svenpetersen1965/VIC-20-Hyper-Expander/Rev. 0/pictures/6766_Hyper_Expander_in_tfw8bit_case.JPG

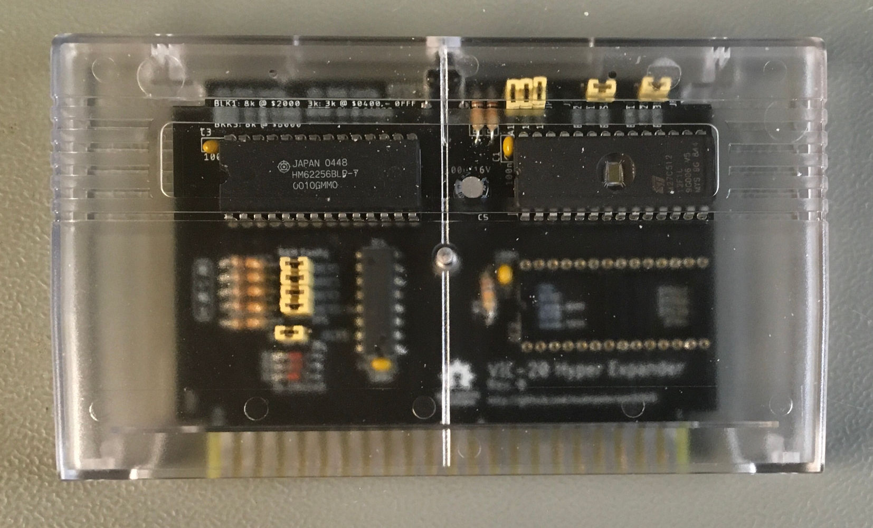
Rev. 0/pictures/6766_Hyper_Expander_in_tfw8bit_case.JPG
