svenpetersen1965/VIC-20-Hyper-Expander/Rev. 1/pictures/8315_-_DOOM.JPG

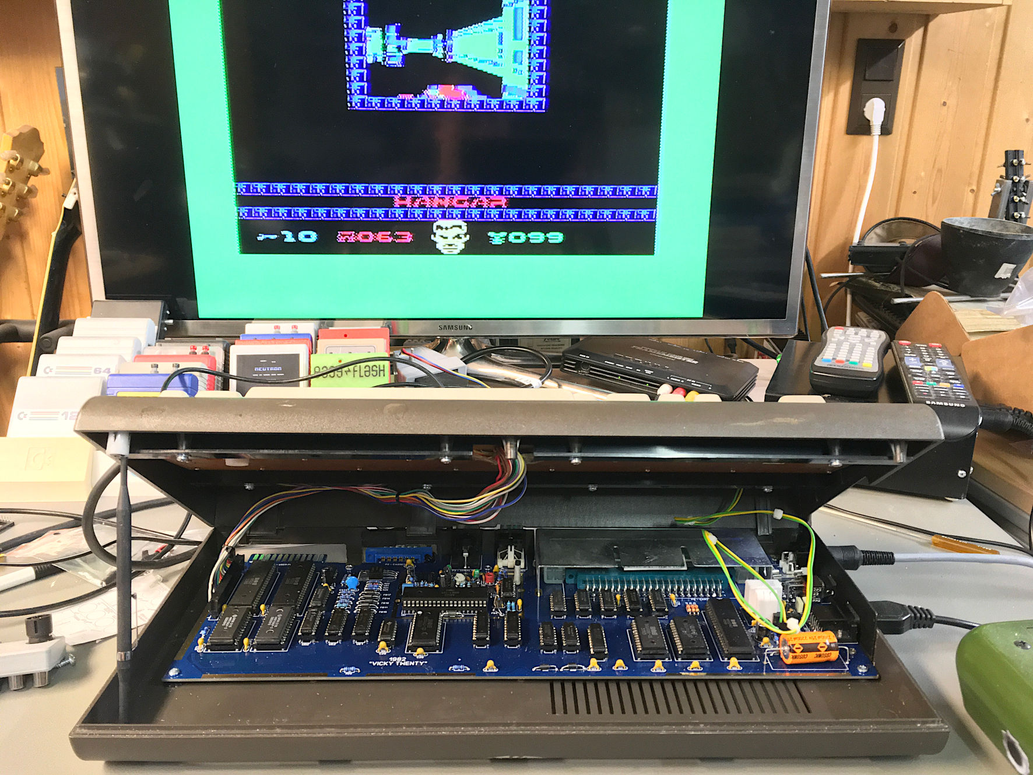
Rev. 1/pictures/8315_-_DOOM.JPG
