svenpetersen1965/VIC-20-Hyper-Expander/Rev. 2/pictures/9388_-_Hyper_Expander_v2_RAMonly.JPG

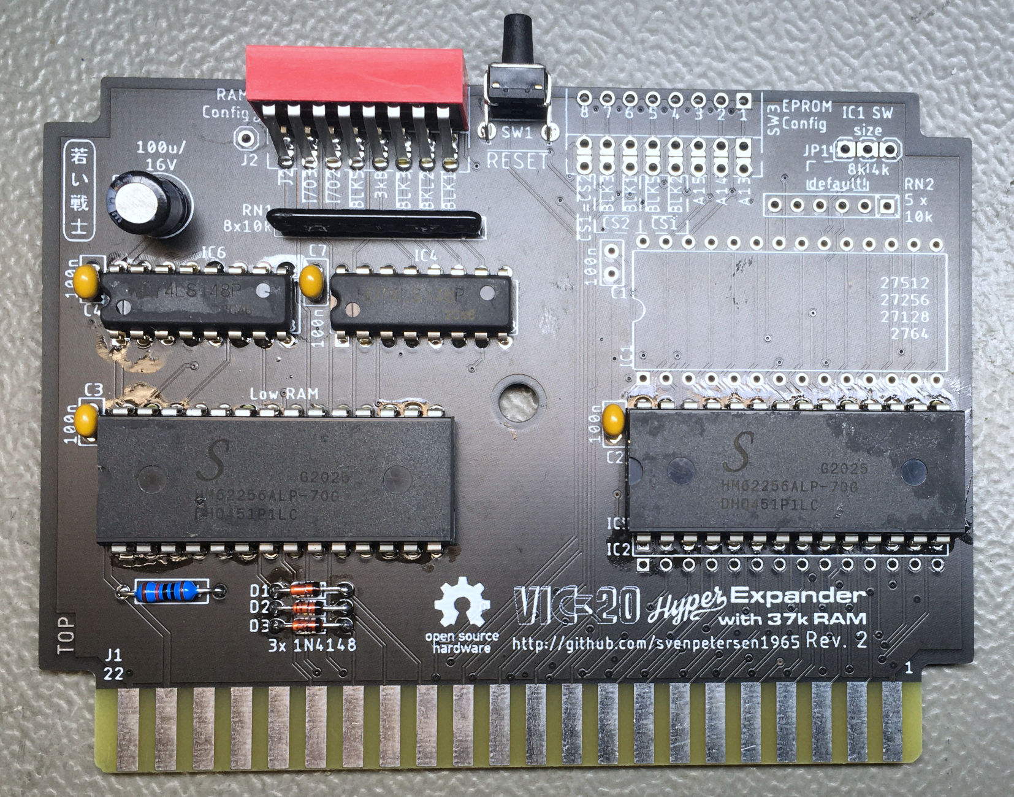
Rev. 2/pictures/9388_-_Hyper_Expander_v2_RAMonly.JPG
