svenpetersen1965/VIC-20-Hyper-Expander/Rev. 2/pictures/9523_-_case_cutout.JPG

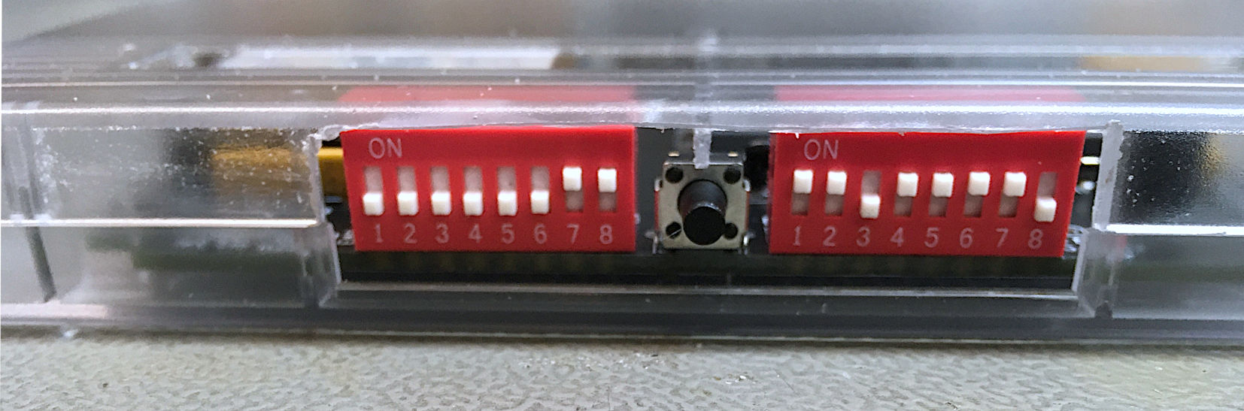
Rev. 2/pictures/9523_-_case_cutout.JPG
