svenpetersen1965/VIC-20-Hyper-Expander/Rev. 2/pictures/9525_-_case_connector.JPG

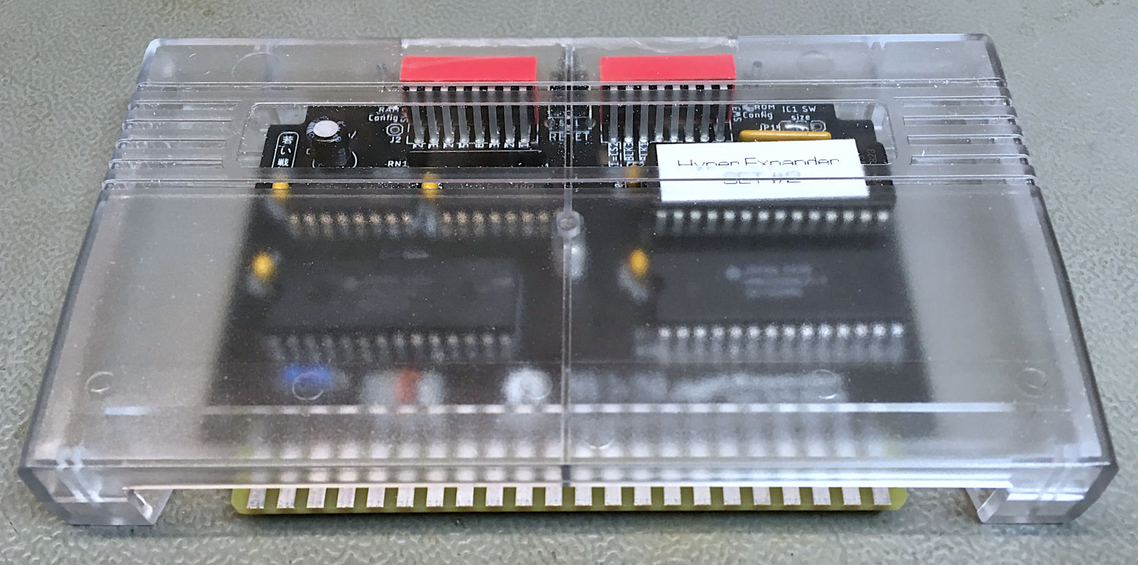
Rev. 2/pictures/9525_-_case_connector.JPG
