svenpetersen1965/VIC-20-Hyper-Expander/Rev. 2/pictures/9766_-_single_in_case.JPG

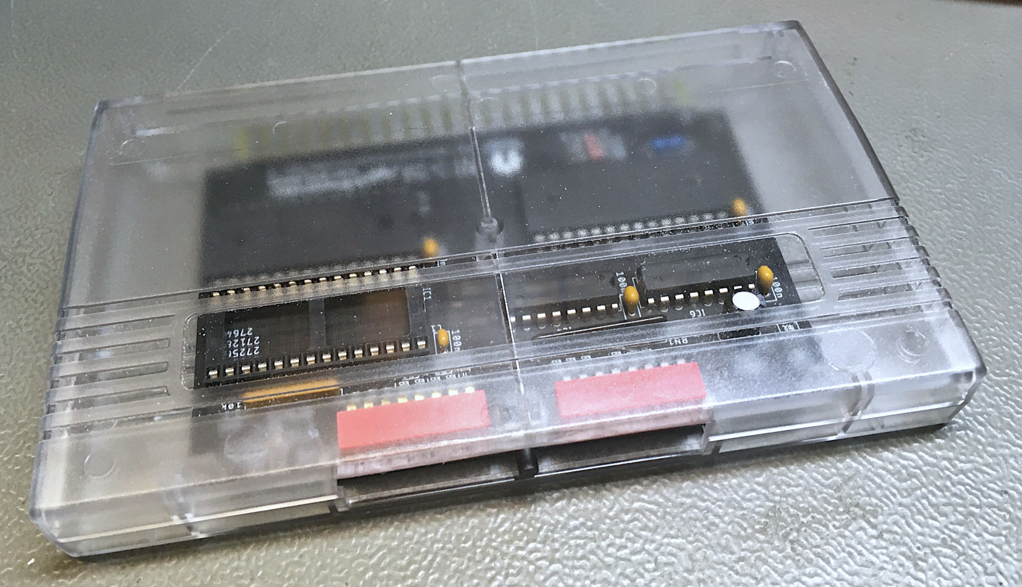
Rev. 2/pictures/9766_-_single_in_case.JPG
