svenpetersen1965/VIC-20-Hyper-Expander/Rev. 2/pictures/BASIC_FORTH_VICTERM.jpg

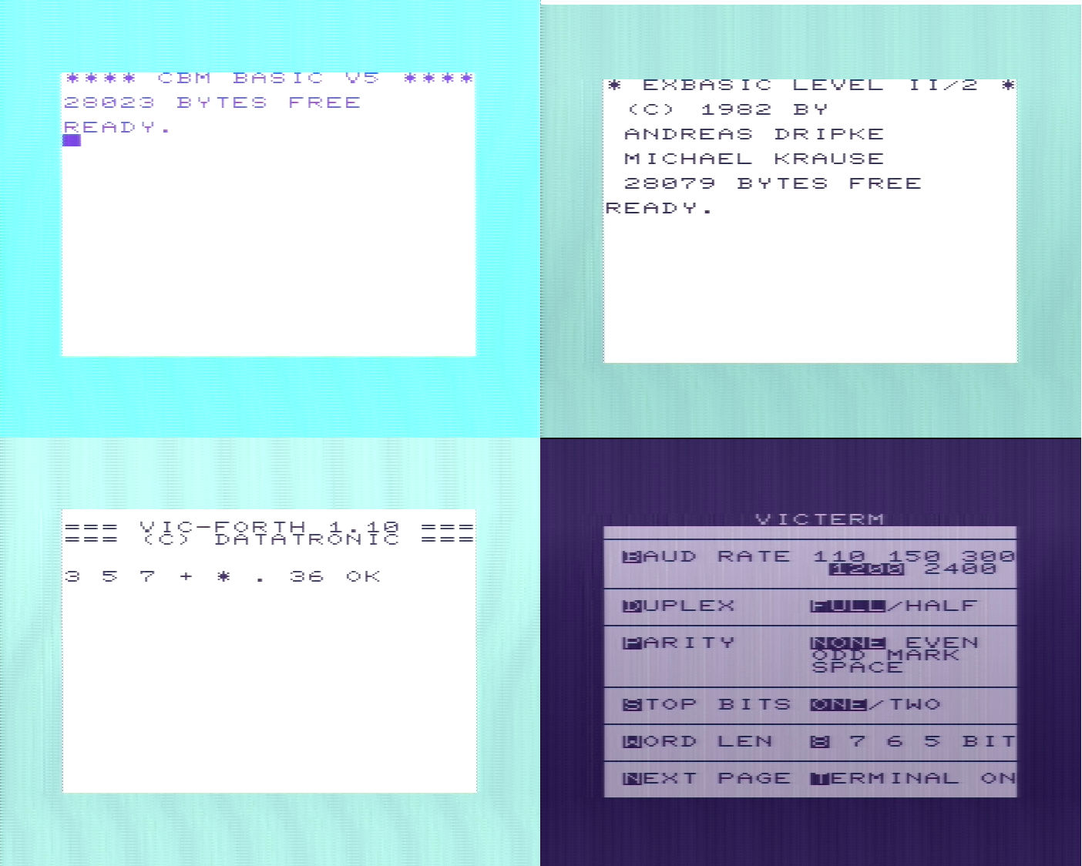
Rev. 2/pictures/BASIC_FORTH_VICTERM.jpg
