svenpetersen1965/VIC-20-Hyper-Expander/Rev. 2/pictures/BASIC_V5.png

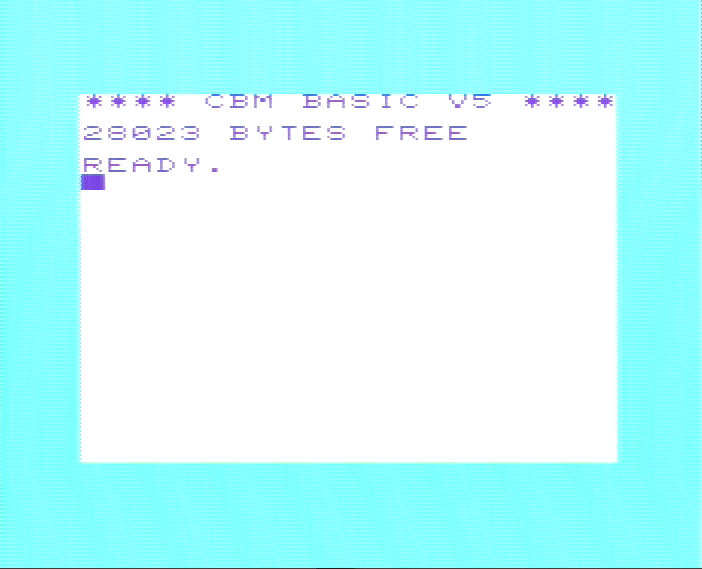
Rev. 2/pictures/BASIC_V5.png
