svenpetersen1965/VIC-20-Hyper-Expander/Rev. 2/pictures/buck_def_load_mspac.jpg

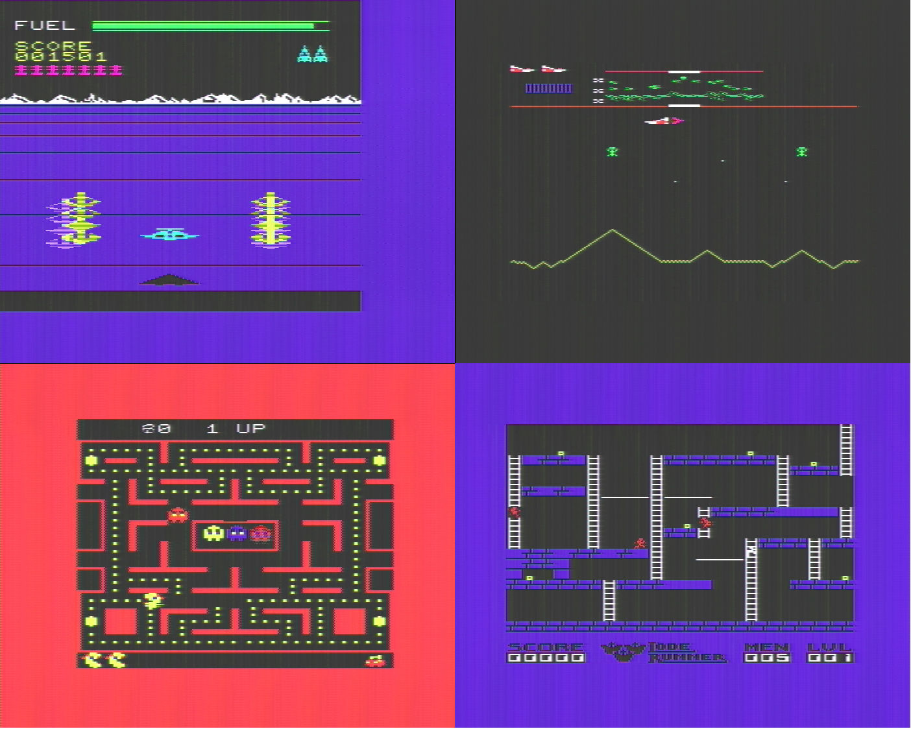
Rev. 2/pictures/buck_def_load_mspac.jpg
