svenpetersen1965/VIC-20-Hyper-Expander/Rev. 2/pictures/buckrogers.png

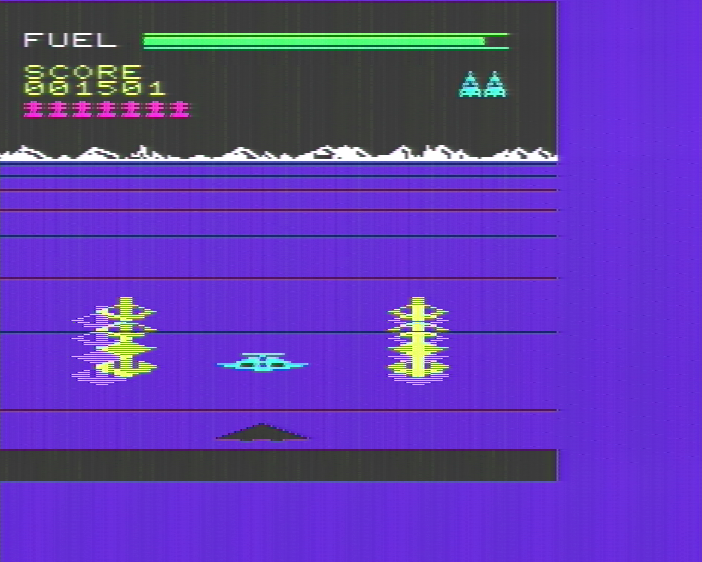
Rev. 2/pictures/buckrogers.png
