svenpetersen1965/VIC-20-Hyper-Expander/Rev. 2/pictures/ExBASIC_L2.png

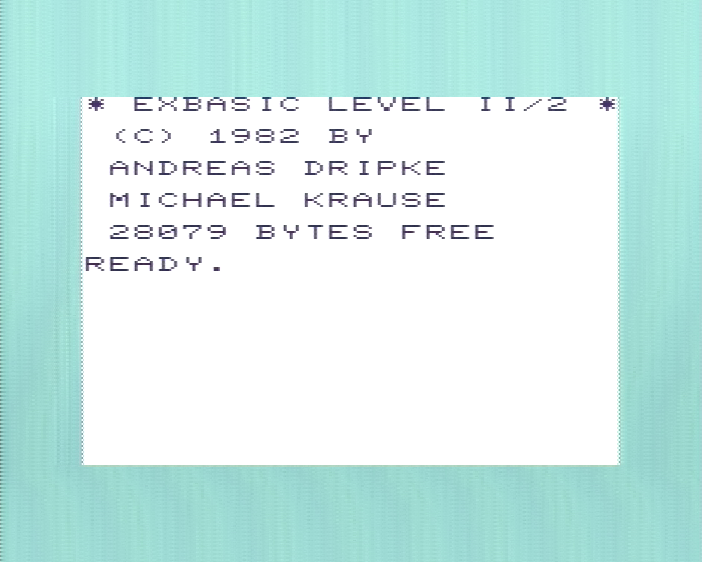
Rev. 2/pictures/ExBASIC_L2.png
