svenpetersen1965/VIC-20-Hyper-Expander/Rev. 2/pictures/mspacman.png

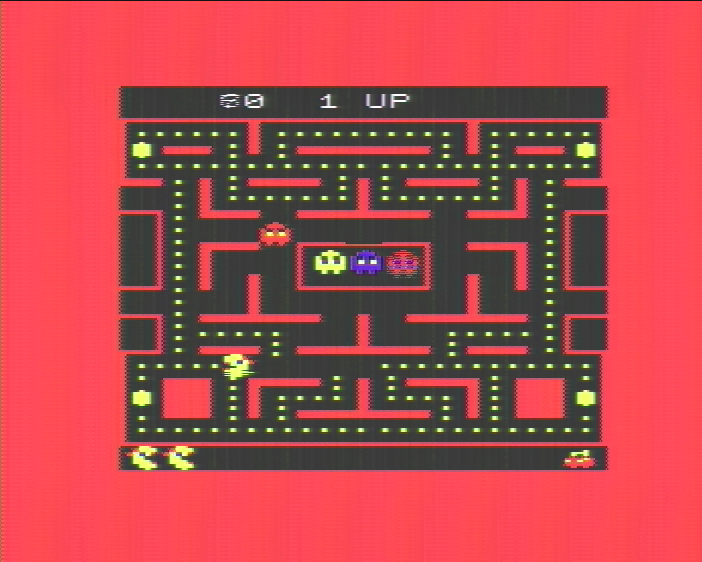
Rev. 2/pictures/mspacman.png
