svenpetersen1965/VIC-20-Hyper-Expander/Rev. 2/pictures/SExp_Diag.jpg

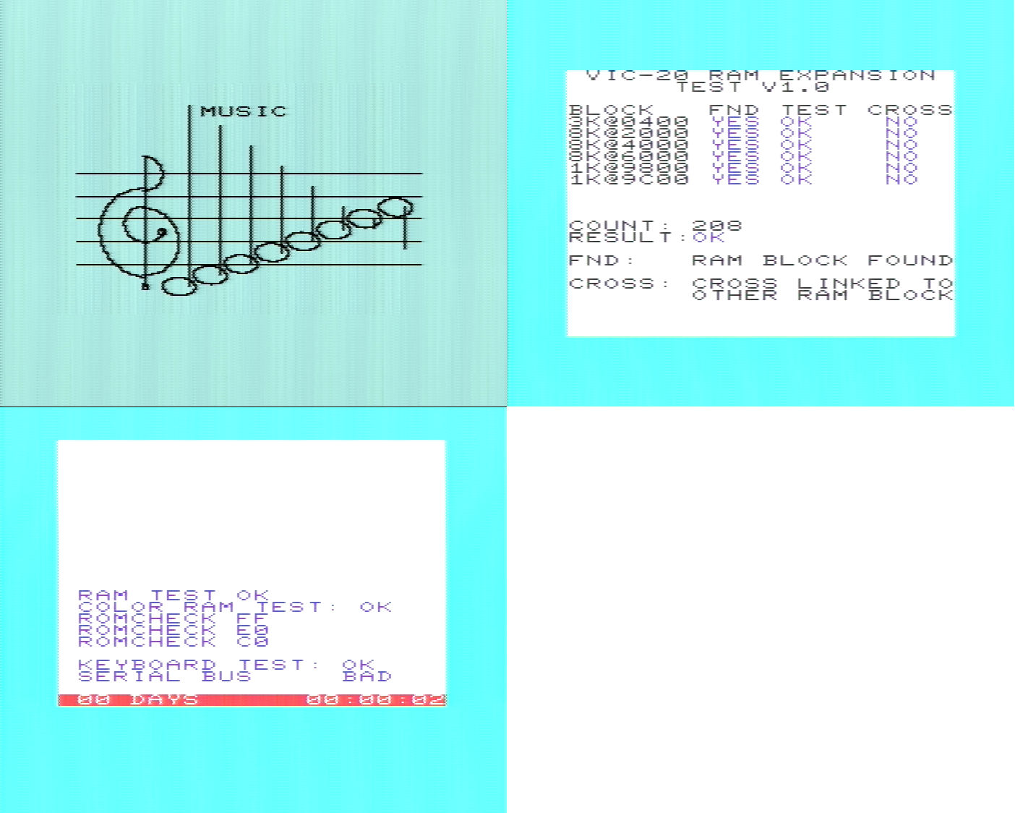
Rev. 2/pictures/SExp_Diag.jpg
