svenpetersen1965/VIC-20-Hyper-Expander/Rev. 2/pictures/vic20diag.png

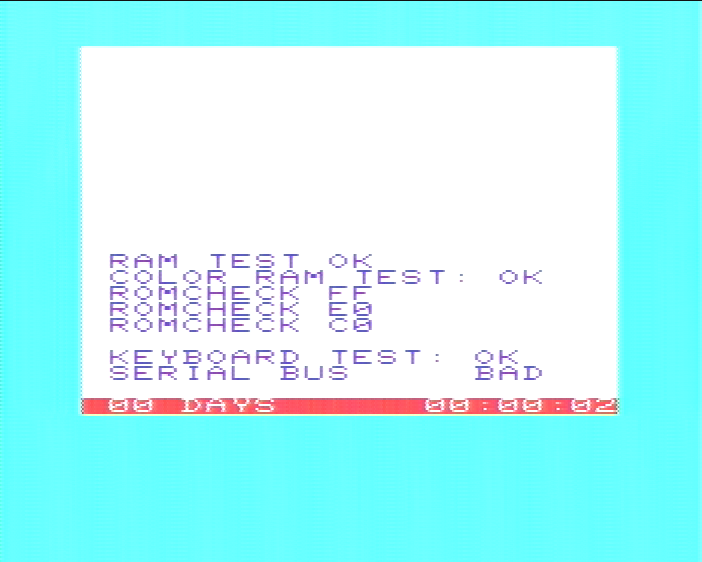
Rev. 2/pictures/vic20diag.png
