svenpetersen1965/VIC-20-Hyper-Expander/Rev. 2/pictures/VIC-FORTH.png

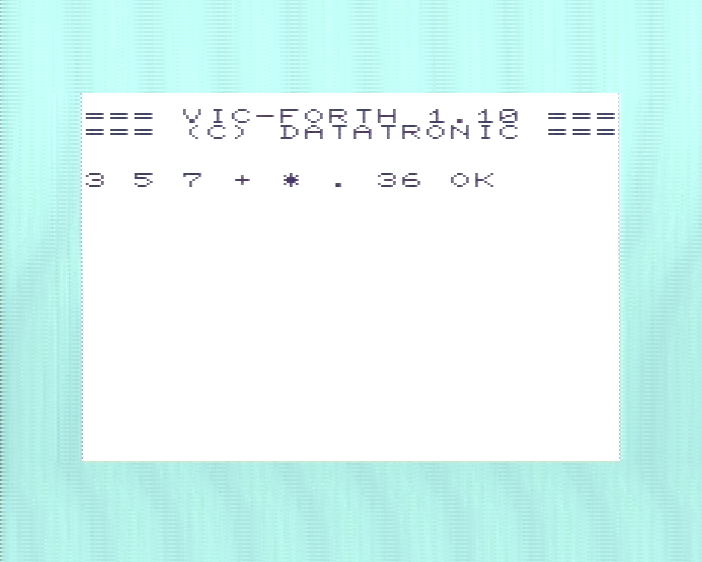
Rev. 2/pictures/VIC-FORTH.png
