svenpetersen1965/VIC-20-Hyper-Expander/Rev. 1/pictures/8356_-_Super_Expander_Software_Test.JPG

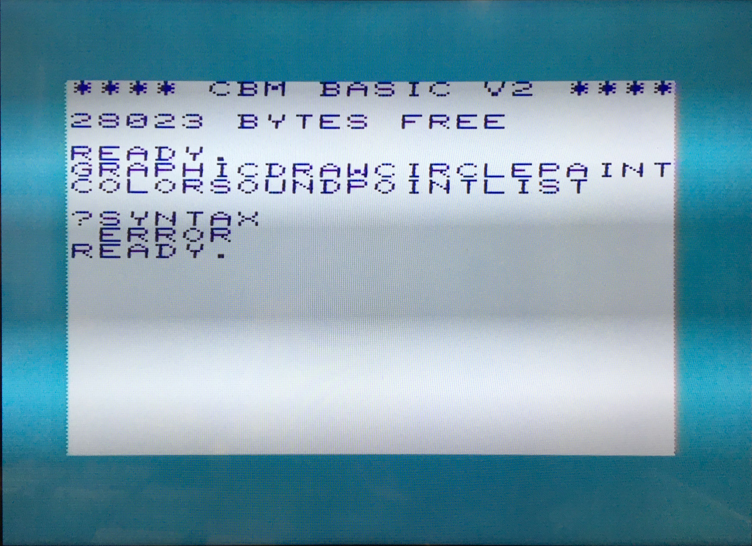
Rev. 1/pictures/8356_-_Super_Expander_Software_Test.JPG
